Nevius43/Radiation-Detector/Firmware/Radiation_Detector/src/RadScan.png

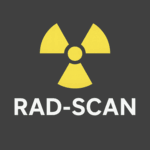
Firmware/Radiation_Detector/src/RadScan.png
