Nevius43/Radiation-Detector/User Interface/SquareLineFiles/cache/thumb_937189207star.png

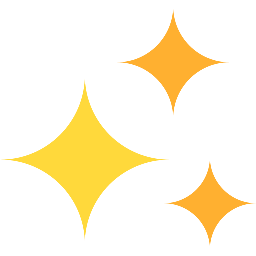
User Interface/SquareLineFiles/cache/thumb_937189207star.png
