Nevius43/Radiation-Detector/User Interface/SquareLineFiles/cache/thumb_1575458026gear.png

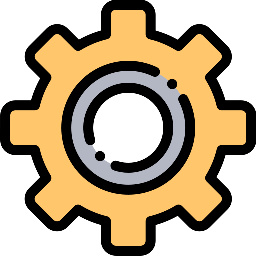
User Interface/SquareLineFiles/cache/thumb_1575458026gear.png
