Nevius43/Radiation-Detector/PCB/RadiationDetector/3D/3314J-1-202E.STEP

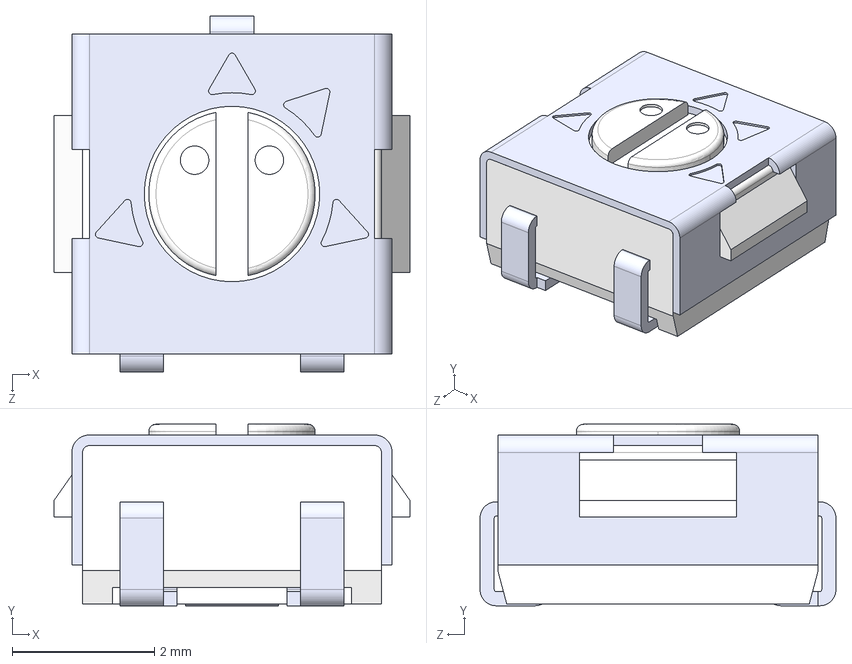
[picture p22: CAD file, 2025-07-28]
PCB/RadiationDetector/3D/3314J-1-202E.STEP
5.00 x 2.55 x 5.00 mm
