Nevius43/Radiation-Detector/PCB/RadiationDetector/3D/PTS645SL43SMTR92-LFS.STEP

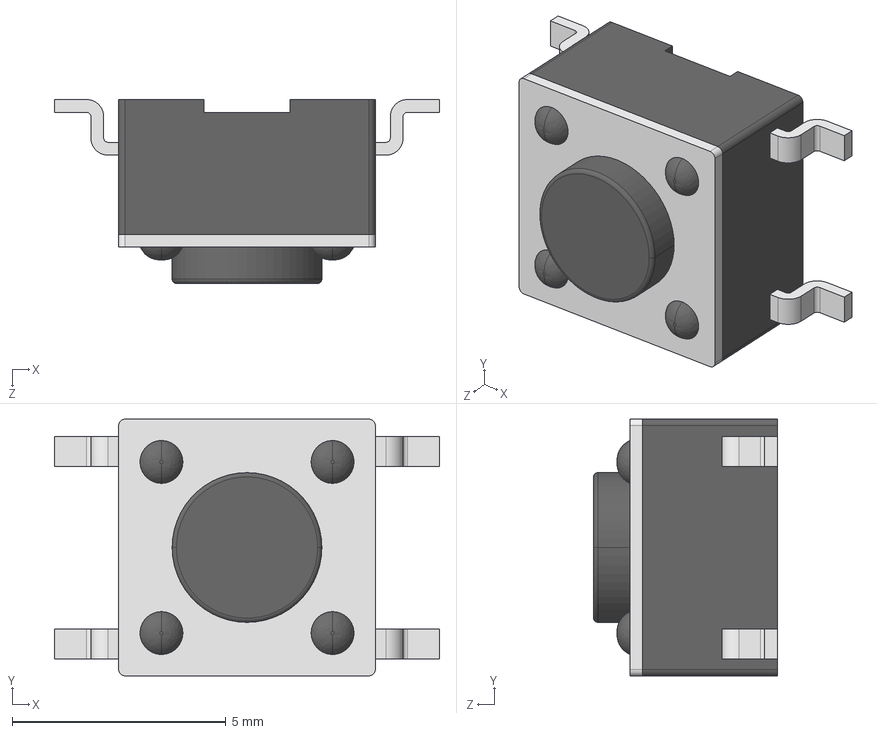
[picture p23: CAD file, 2025-07-28]
PCB/RadiationDetector/3D/PTS645SL43SMTR92-LFS.STEP
9.00 x 6.00 x 4.30 mm
