Nevius43/Radiation-Detector/PCB/RadiationDetector/3D/48102SC.stp

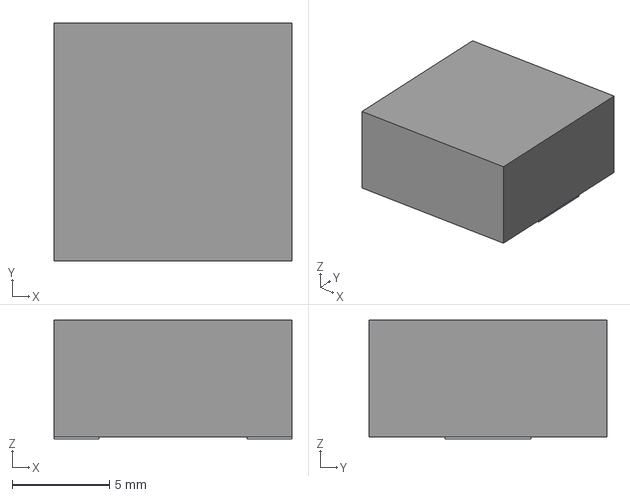
[picture p24: CAD file, 2025-07-28]
PCB/RadiationDetector/3D/48102SC.stp
12.2 x 12.2 x 6.10 mm
Pins
