Nevius43/Radiation-Detector/Firmware/Radiation_Detector/src/ui_font_Pixel.c

/*******************************************************************************
 * Size: 30 px
 * Bpp: 1
 * Opts: --bpp 1 --size 30 --font C:/Users/pablo/OneDrive/Documentos/GitHub/Radiation-Detector/User Interface/SquareLineFiles/assets/VCR_OSD_MONO.ttf -o C:/Users/pablo/OneDrive/Documentos/GitHub/Radiation-Detector/User Interface/SquareLineFiles/assets\ui_font_Pixel.c --format lvgl -r 0x20-0x7f --no-compress --no-prefilter
 ******************************************************************************/

#include "ui.h"

#ifndef UI_FONT_PIXEL
#define UI_FONT_PIXEL 1
#endif

#if UI_FONT_PIXEL

/*-----------------
 *    BITMAPS
 *----------------*/

/*Store the image of the glyphs*/
static LV_ATTRIBUTE_LARGE_CONST const uint8_t glyph_bitmap[] = {
    /* U+0020 " " */
    0x0,

    /* U+0021 "!" */
    0xff, 0xff, 0xff, 0xff, 0xff, 0xf8, 0x3, 0xfe,

    /* U+0022 "\"" */
    0xf0, 0xff, 0xf, 0xf0, 0xff, 0xf, 0x60, 0x66,
    0x6,

    /* U+0023 "#" */
    0x0, 0x70, 0x38, 0xe0, 0x71, 0xc0, 0xe3, 0xf1,
    0xc7, 0xe3, 0xff, 0xff, 0xfc, 0x7f, 0xf8, 0xfc,
    0x70, 0x38, 0xe0, 0x71, 0xf8, 0xe3, 0xf1, 0xff,
    0xff, 0xfe, 0x3f, 0xfc, 0x7e, 0x38, 0x1c, 0x70,
    0x38, 0xe0, 0x70, 0x0,

    /* U+0024 "$" */
    0x3, 0x80, 0x3f, 0xe0, 0x7f, 0xc1, 0xff, 0xc3,
    0xbb, 0x9f, 0x77, 0xfe, 0xef, 0xf1, 0xc7, 0xfb,
    0x80, 0x7f, 0xe0, 0x7f, 0xc0, 0xff, 0xc0, 0x3b,
    0xfc, 0x71, 0xfe, 0xef, 0xfd, 0xdf, 0x3f, 0xf8,
    0x7f, 0xf0, 0x7f, 0xc0, 0x1c, 0x0, 0x38, 0x0,

    /* U+0025 "%" */
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
    0x9e, 0x7, 0xf8, 0x3, 0xf0, 0x7,

    /* U+0079 "y" */
    0xe0, 0xf, 0xc0, 0x1f, 0x80, 0x3f, 0x1, 0xfe,
    0x3, 0xfc, 0x7, 0xf8, 0x1f, 0xfc, 0xff, 0xf9,
    0xfe, 0xff, 0x9c, 0x7e, 0x38, 0xfc, 0x70, 0x0,
    0xe0, 0x7, 0xc0, 0xf, 0x8f, 0xfe, 0x1f, 0xfc,
    0x3f, 0xe0,

    /* U+007A "z" */
    0xff, 0xff, 0xff, 0xff, 0xff, 0xc0, 0xf, 0x0,
    0x78, 0x1, 0xe0, 0xf, 0x0, 0xf0, 0x7, 0x80,
    0x1e, 0x1, 0xe0, 0xf, 0x0, 0x3c, 0x3, 0xff,
    0xff, 0xff, 0xff, 0xff,

    /* U+007B "{" */
    0x7, 0x83, 0xc1, 0xe3, 0xf1, 0xc0, 0xe0, 0x70,
    0x38, 0x1c, 0xe, 0x3c, 0x1e, 0xf, 0x0, 0xe0,
    0x70, 0x38, 0x1c, 0xe, 0x7, 0x3, 0x81, 0xf8,
    0x3c, 0x1e, 0xf,

    /* U+007C "|" */
    0xff, 0xff, 0xff, 0xff, 0xff, 0xff, 0xff, 0xff,
    0xff,

    /* U+007D "}" */
    0xf0, 0x78, 0x3c, 0x1f, 0x81, 0xc0, 0xe0, 0x70,
    0x38, 0x1c, 0xe, 0x1, 0xe0, 0xf0, 0x78, 0xe0,
    0x70, 0x38, 0x1c, 0xe, 0x7, 0x3, 0x8f, 0xc7,
    0x83, 0xc1, 0xe0,

    /* U+007E "~" */
    0x1e, 0x4, 0xfe, 0x73, 0xf9, 0xf9, 0xfc, 0xc0,
    0xe3, 0x3, 0x80
};


/*---------------------
 *  GLYPH DESCRIPTION
 *--------------------*/

static const lv_font_fmt_txt_glyph_dsc_t glyph_dsc[] = {
    {.bitmap_index = 0, .adv_w = 0, .box_w = 0, .box_h = 0, .ofs_x = 0, .ofs_y = 0} /* id = 0 reserved */,
    {.bitmap_index = 0, .adv_w = 281, .box_w = 1, .box_h = 1, .ofs_x = 0, .ofs_y = 0},
    {.bitmap_index = 1, .adv_w = 281, .box_w = 3, .box_h = 21, .ofs_x = 6, .ofs_y = 2},
    {.bitmap_index = 9, .adv_w = 281, .box_w = 12, .box_h = 6, .ofs_x = 3, .ofs_y = 17},
    {.bitmap_index = 18, .adv_w = 281, .box_w = 15, .box_h = 19, .ofs_x = 1, .ofs_y = 4},
    {.bitmap_index = 54, .adv_w = 281, .box_w = 15, .box_h = 21, .ofs_x = 1, .ofs_y = 2},
    {.bitmap_index = 94, .adv_w = 281, .box_w = 15, .box_h = 21, .ofs_x = 1, .ofs_y = 2},
    {.bitmap_index = 134, .adv_w = 281, .box_w = 15, .box_h = 24, .ofs_x = 1, .ofs_y = 2},
    {.bitmap_index = 179, .adv_w = 281, .box_w = 4, .box_h = 6, .ofs_x = 6, .ofs_y = 17},
    {.bitmap_index = 182, .adv_w = 281, .box_w = 7, .box_h = 24, .ofs_x = 4, .ofs_y = 2},
    {.bitmap_index = 203, .adv_w = 281, .box_w = 7, .box_h = 24, .ofs_x = 6, .ofs_y = 2},
    {.bitmap_index = 224, .adv_w = 281, .box_w = 12, .box_h = 13, .ofs_x = 3, .ofs_y = 11},
    {.bitmap_index = 244, .adv_w = 281, .box_w = 15, .box_h = 15, .ofs_x = 1, .ofs_y = 5},
    {.bitmap_index = 273, .adv_w = 281, .box_w = 6, .box_h = 6, .ofs_x = 4, .ofs_y = 2},
    {.bitmap_index = 278, .adv_w = 281, .box_w = 12, .box_h = 3, .ofs_x = 3, .ofs_y = 11},
    {.bitmap_index = 283, .adv_w = 281, .box_w = 3, .box_h = 3, .ofs_x = 6, .ofs_y = 2},
    {.bitmap_index = 285, .adv_w = 281, .box_w = 15, .box_h = 21, .ofs_x = 1, .ofs_y = 2},
    {.bitmap_index = 325, .adv_w = 281, .box_w = 15, .box_h = 21, .ofs_x = 1, .ofs_y = 2},
    {.bitmap_index = 365, .adv_w = 281, .box_w = 9, .box_h = 21, .ofs_x = 4, .ofs_y = 2},
    {.bitmap_index = 389, .adv_w = 281, .box_w = 15, .box_h = 21, .ofs_x = 1, .ofs_y = 2},
    {.bitmap_index = 429, .adv_w = 281, .box_w = 15, .box_h = 21, .ofs_x = 1, .ofs_y = 2},
    {.bitmap_index = 469, .adv_w = 281, .box_w = 15, .box_h = 21, .ofs_x = 1, .ofs_y = 2},
    {.bitmap_index = 509, .adv_w = 281, .box_w = 15, .box_h = 21, .ofs_x = 1, .ofs_y = 2},
    {.bitmap_index = 549, .adv_w = 281, .box_w = 15, .box_h = 21, .ofs_x = 1, .ofs_y = 2},
    {.bitmap_index = 589, .adv_w = 281, .box_w = 15, .box_h = 21, .ofs_x = 1, .ofs_y = 2},
    {.bitmap_index = 629, .adv_w = 281, .box_w = 15, .box_h = 21, .ofs_x = 1, .ofs_y = 2},
    {.bitmap_index = 669, .adv_w = 281, .box_w = 15, .box_h = 21, .ofs_x = 1, .ofs_y = 2},
    {.bitmap_index = 709, .adv_w = 281, .box_w = 3, .box_h = 15, .ofs_x = 6, .ofs_y = 5},
    {.bitmap_index = 715, .adv_w = 281, .box_w = 6, .box_h = 18, .ofs_x = 3, .ofs_y = 1},
    {.bitmap_index = 729, .adv_w = 281, .box_w = 12, .box_h = 23, .ofs_x = 3, .ofs_y = 2},
    {.bitmap_index = 764, .adv_w = 281, .box_w = 15, .box_h = 9, .ofs_x = 1, .ofs_y = 8},
    {.bitmap_index = 781, .adv_w = 281, .box_w = 12, .box_h = 23, .ofs_x = 3, .ofs_y = 2},
    {.bitmap_index = 816, .adv_w = 281, .box_w = 15, .box_h = 21, .ofs_x = 1, .ofs_y = 2},
    {.bitmap_index = 856, .adv_w = 281, .box_w = 15, .box_h = 18, .ofs_x = 1, .ofs_y = 3},
    {.bitmap_index = 890, .adv_w = 281, .box_w = 15, .box_h = 21, .ofs_x = 1, .ofs_y = 2},
    {.bitmap_index = 930, .adv_w = 281, .box_w = 15, .box_h = 21, .ofs_x = 1, .ofs_y = 2},
    {.bitmap_index = 970, .adv_w = 281, .box_w = 15, .box_h = 21, .ofs_x = 1, .ofs_y = 2},
    {.bitmap_index = 1010, .adv_w = 281, .box_w = 15, .box_h = 21, .ofs_x = 1, .ofs_y = 2},
    {.bitmap_index = 1050, .adv_w = 281, .box_w = 15, .box_h = 21, .ofs_x = 1, .ofs_y = 2},
    {.bitmap_index = 1090, .adv_w = 281, .box_w = 15, .box_h = 21, .ofs_x = 1, .ofs_y = 2},
    {.bitmap_index = 1130, .adv_w = 281, .box_w = 15, .box_h = 21, .ofs_x = 1, .ofs_y = 2},
    {.bitmap_index = 1170, .adv_w = 281, .box_w = 15, .box_h = 21, .ofs_x = 1, .ofs_y = 2},
    {.bitmap_index = 1210, .adv_w = 281, .box_w = 9, .box_h = 21, .ofs_x = 4, .ofs_y = 2},
    {.bitmap_index = 1234, .adv_w = 281, .box_w = 15, .box_h = 21, .ofs_x = 1, .ofs_y = 2},
    {.bitmap_index = 1274, .adv_w = 281, .box_w = 15, .box_h = 21, .ofs_x = 1, .ofs_y = 2},
    {.bitmap_index = 1314, .adv_w = 281, .box_w = 15, .box_h = 21, .ofs_x = 1, .ofs_y = 2},
    {.bitmap_index = 1354, .adv_w = 281, .box_w = 15, .box_h = 21, .ofs_x = 1, .ofs_y = 2},
    {.bitmap_index = 1394, .adv_w = 281, .box_w = 15, .box_h = 21, .ofs_x = 1, .ofs_y = 2},
    {.bitmap_index = 1434, .adv_w = 281, .box_w = 15, .box_h = 21, .ofs_x = 1, .ofs_y = 2},
    {.bitmap_index = 1474, .adv_w = 281, .box_w = 15, .box_h = 21, .ofs_x = 1, .ofs_y = 2},
    {.bitmap_index = 1514, .adv_w = 281, .box_w = 15, .box_h = 21, .ofs_x = 1, .ofs_y = 2},
    {.bitmap_index = 1554, .adv_w = 281, .box_w = 15, .box_h = 21, .ofs_x = 1, .ofs_y = 2},
    {.bitmap_index = 1594, .adv_w = 281, .box_w = 15, .box_h = 21, .ofs_x = 1, .ofs_y = 2},
    {.bitmap_index = 1634, .adv_w = 281, .box_w = 15, .box_h = 21, .ofs_x = 1, .ofs_y = 2},
    {.bitmap_index = 1674, .adv_w = 281, .box_w = 15, .box_h = 21, .ofs_x = 1, .ofs_y = 2},
    {.bitmap_index = 1714, .adv_w = 281, .box_w = 15, .box_h = 21, .ofs_x = 1, .ofs_y = 2},
    {.bitmap_index = 1754, .adv_w = 281, .box_w = 15, .box_h = 21, .ofs_x = 1, .ofs_y = 2},
    {.bitmap_index = 1794, .adv_w = 281, .box_w = 15, .box_h = 21, .ofs_x = 1, .ofs_y = 2},
    {.bitmap_index = 1834, .adv_w = 281, .box_w = 15, .box_h = 21, .ofs_x = 1, .ofs_y = 2},
    {.bitmap_index = 1874, .adv_w = 281, .box_w = 15, .box_h = 21, .ofs_x = 1, .ofs_y = 2},
    {.bitmap_index = 1914, .adv_w = 281, .box_w = 9, .box_h = 24, .ofs_x = 6, .ofs_y = 2},
    {.bitmap_index = 1941, .adv_w = 281, .box_w = 15, .box_h = 21, .ofs_x = 1, .ofs_y = 2},
    {.bitmap_index = 1981, .adv_w = 281, .box_w = 9, .box_h = 24, .ofs_x = 3, .ofs_y = 2},
    {.bitmap_index = 2008, .adv_w = 281, .box_w = 14, .box_h = 7, .ofs_x = 1, .ofs_y = 15},
    {.bitmap_index = 2021, .adv_w = 281, .box_w = 18, .box_h = 3, .ofs_x = 0, .ofs_y = 0},
    {.bitmap_index = 2028, .adv_w = 281, .box_w = 7, .box_h = 5, .ofs_x = 4, .ofs_y = 18},
    {.bitmap_index = 2033, .adv_w = 281, .box_w = 15, .box_h = 18, .ofs_x = 1, .ofs_y = 2},
    {.bitmap_index = 2067, .adv_w = 281, .box_w = 15, .box_h = 21, .ofs_x = 1, .ofs_y = 2},
    {.bitmap_index = 2107, .adv_w = 281, .box_w = 15, .box_h = 16, .ofs_x = 1, .ofs_y = 2},
    {.bitmap_index = 2137, .adv_w = 281, .box_w = 15, .box_h = 21, .ofs_x = 1, .ofs_y = 2},
    {.bitmap_index = 2177, .adv_w = 281, .box_w = 14, .box_h = 16, .ofs_x = 1, .ofs_y = 2},
    {.bitmap_index = 2205, .adv_w = 281, .box_w = 12, .box_h = 21, .ofs_x = 3, .ofs_y = 2},
    {.bitmap_index = 2237, .adv_w = 281, .box_w = 15, .box_h = 18, .ofs_x = 1, .ofs_y = 2},
    {.bitmap_index = 2271, .adv_w = 281, .box_w = 15, .box_h = 21, .ofs_x = 1, .ofs_y = 2},
    {.bitmap_index = 2311, .adv_w = 281, .box_w = 9, .box_h = 20, .ofs_x = 4, .ofs_y = 2},
    {.bitmap_index = 2334, .adv_w = 281, .box_w = 9, .box_h = 23, .ofs_x = 4, .ofs_y = 2},
    {.bitmap_index = 2360, .adv_w = 281, .box_w = 15, .box_h = 21, .ofs_x = 1, .ofs_y = 2},
    {.bitmap_index = 2400, .adv_w = 281, .box_w = 3, .box_h = 21, .ofs_x = 7, .ofs_y = 2},
    {.bitmap_index = 2408, .adv_w = 281, .box_w = 15, .box_h = 16, .ofs_x = 1, .ofs_y = 2},
    {.bitmap_index = 2438, .adv_w = 281, .box_w = 15, .box_h = 16, .ofs_x = 1, .ofs_y = 2},
    {.bitmap_index = 2468, .adv_w = 281, .box_w = 15, .box_h = 16, .ofs_x = 1, .ofs_y = 2},
    {.bitmap_index = 2498, .adv_w = 281, .box_w = 15, .box_h = 18, .ofs_x = 1, .ofs_y = 2},
    {.bitmap_index = 2532, .adv_w = 281, .box_w = 15, .box_h = 18, .ofs_x = 1, .ofs_y = 2},
    {.bitmap_index = 2566, .adv_w = 281, .box_w = 15, .box_h = 16, .ofs_x = 1, .ofs_y = 2},
    {.bitmap_index = 2596, .adv_w = 281, .box_w = 14, .box_h = 16, .ofs_x = 1, .ofs_y = 2},
    {.bitmap_index = 2624, .adv_w = 281, .box_w = 9, .box_h = 21, .ofs_x = 4, .ofs_y = 2},
    {.bitmap_index = 2648, .adv_w = 281, .box_w = 15, .box_h = 16, .ofs_x = 1, .ofs_y = 2},
    {.bitmap_index = 2678, .adv_w = 281, .box_w = 15, .box_h = 16, .ofs_x = 1, .ofs_y = 2},
    {.bitmap_index = 2708, .adv_w = 281, .box_w = 15, .box_h = 16, .ofs_x = 1, .ofs_y = 2},
    {.bitmap_index = 2738, .adv_w = 281, .box_w = 15, .box_h = 16, .ofs_x = 1, .ofs_y = 2},
    {.bitmap_index = 2768, .adv_w = 281, .box_w = 15, .box_h = 18, .ofs_x = 1, .ofs_y = 2},
    {.bitmap_index = 2802, .adv_w = 281, .box_w = 14, .box_h = 16, .ofs_x = 1, .ofs_y = 2},
    {.bitmap_index = 2830, .adv_w = 281, .box_w = 9, .box_h = 24, .ofs_x = 4, .ofs_y = 2},
    {.bitmap_index = 2857, .adv_w = 281, .box_w = 3, .box_h = 24, .ofs_x = 7, .ofs_y = 2},
    {.bitmap_index = 2866, .adv_w = 281, .box_w = 9, .box_h = 24, .ofs_x = 4, .ofs_y = 2},
    {.bitmap_index = 2893, .adv_w = 281, .box_w = 14, .box_h = 6, .ofs_x = 1, .ofs_y = 9}
};

/*---------------------
 *  CHARACTER MAPPING
 *--------------------*/



/*Collect the unicode lists and glyph_id offsets*/
static const lv_font_fmt_txt_cmap_t cmaps[] =
{
    {
        .range_start = 32, .range_length = 95, .glyph_id_start = 1,
        .unicode_list = NULL, .glyph_id_ofs_list = NULL, .list_length = 0, .type = LV_FONT_FMT_TXT_CMAP_FORMAT0_TINY
    }
};



/*--------------------
 *  ALL CUSTOM DATA
 *--------------------*/

#if LVGL_VERSION_MAJOR == 8
/*Store all the custom data of the font*/
static  lv_font_fmt_txt_glyph_cache_t cache;
#endif

#if LVGL_VERSION_MAJOR >= 8
static const lv_font_fmt_txt_dsc_t font_dsc = {
#else
static lv_font_fmt_txt_dsc_t font_dsc = {
#endif
    .glyph_bitmap = glyph_bitmap,
    .glyph_dsc = glyph_dsc,
    .cmaps = cmaps,
    .kern_dsc = NULL,
    .kern_scale = 0,
    .cmap_num = 1,
    .bpp = 1,
    .kern_classes = 0,
    .bitmap_format = 0,
#if LVGL_VERSION_MAJOR == 8
    .cache = &cache
#endif
};



/*-----------------
 *  PUBLIC FONT
 *----------------*/

/*Initialize a public general font descriptor*/
#if LVGL_VERSION_MAJOR >= 8
const lv_font_t ui_font_Pixel = {
#else
lv_font_t ui_font_Pixel = {
#endif
    .get_glyph_dsc = lv_font_get_glyph_dsc_fmt_txt,    /*Function pointer to get glyph's data*/
    .get_glyph_bitmap = lv_font_get_bitmap_fmt_txt,    /*Function pointer to get glyph's bitmap*/
    .line_height = 26,          /*The maximum line height required by the font*/
    .base_line = 0,             /*Baseline measured from the bottom of the line*/
#if !(LVGL_VERSION_MAJOR == 6 && LVGL_VERSION_MINOR == 0)
    .subpx = LV_FONT_SUBPX_NONE,
#endif
#if LV_VERSION_CHECK(7, 4, 0) || LVGL_VERSION_MAJOR >= 8
    .underline_position = -3,
    .underline_thickness = 2,
#endif
    .dsc = &font_dsc,          /*The custom font data. Will be accessed by `get_glyph_bitmap/dsc` */
#if LV_VERSION_CHECK(8, 2, 0) || LVGL_VERSION_MAJOR >= 9
    .fallback = NULL,
#endif
    .user_data = NULL,
};



#endif /*#if UI_FONT_PIXEL*/
