Nevius43/Radiation-Detector/Firmware/Radiation_Detector/src/ui_font_Pixel_20.c

/*******************************************************************************
 * Size: 20 px
 * Bpp: 1
 * Opts: --bpp 1 --size 20 --font C:/Users/pablo/OneDrive/Documentos/GitHub/Radiation-Detector/User Interface/SquareLineFiles/assets/VCR_OSD_MONO.ttf -o C:/Users/pablo/OneDrive/Documentos/GitHub/Radiation-Detector/User Interface/SquareLineFiles/assets\ui_font_Pixel_20.c --format lvgl -r 0x20-0x7f --no-compress --no-prefilter
 ******************************************************************************/

#include "ui.h"

#ifndef UI_FONT_PIXEL_20
#define UI_FONT_PIXEL_20 1
#endif

#if UI_FONT_PIXEL_20

/*-----------------
 *    BITMAPS
 *----------------*/

/*Store the image of the glyphs*/
static LV_ATTRIBUTE_LARGE_CONST const uint8_t glyph_bitmap[] = {
    /* U+0020 " " */
    0x0,

    /* U+0021 "!" */
    0xff, 0xff, 0xf0, 0xf0,

    /* U+0022 "\"" */
    0xe7, 0xe7, 0xe7, 0x42,

    /* U+0023 "#" */
    0x3, 0xc, 0xc3, 0x3c, 0xff, 0xff, 0x3c, 0xc3,
    0x30, 0xcf, 0x3f, 0xff, 0xcf, 0x30, 0xcc, 0x30,
    0x0,

    /* U+0024 "$" */
    0xc, 0xf, 0xc7, 0xfb, 0xb7, 0xcc, 0xfb, 0x7,
    0xf0, 0xfe, 0xd, 0xf3, 0x3e, 0xdd, 0xfe, 0x3f,
    0x3, 0x0,

    /* U+0025 "%" */
    0x70, 0xfe, 0x3d, 0x8f, 0x67, 0xfb, 0x9d, 0xc0,
    0xe0, 0x70, 0x3b, 0x9d, 0xfe, 0x6f, 0x1b, 0xc7,
    0xf0, 0xe0,

    /* U+0026 "&" */
    0x1c, 0xf, 0x86, 0x31, 0x8c, 0x63, 0x18, 0xc3,
    0x60, 0xf8, 0x7c, 0x3f, 0xc, 0xef, 0x1f, 0xc3,
    0xb8, 0xe7, 0xfc, 0xfb,

    /* U+0027 "'" */
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

    /* U+007C "|" */
    0xff, 0xff, 0xff, 0xff,

    /* U+007D "}" */
    0xe3, 0x8f, 0xc, 0x30, 0xc3, 0x7, 0x1c, 0xc3,
    0xc, 0x33, 0xce, 0x38,

    /* U+007E "~" */
    0x38, 0x5f, 0x3c, 0xfa, 0x1c
};


/*---------------------
 *  GLYPH DESCRIPTION
 *--------------------*/

static const lv_font_fmt_txt_glyph_dsc_t glyph_dsc[] = {
    {.bitmap_index = 0, .adv_w = 0, .box_w = 0, .box_h = 0, .ofs_x = 0, .ofs_y = 0} /* id = 0 reserved */,
    {.bitmap_index = 0, .adv_w = 188, .box_w = 1, .box_h = 1, .ofs_x = 0, .ofs_y = 0},
    {.bitmap_index = 1, .adv_w = 188, .box_w = 2, .box_h = 14, .ofs_x = 4, .ofs_y = 1},
    {.bitmap_index = 5, .adv_w = 188, .box_w = 8, .box_h = 4, .ofs_x = 2, .ofs_y = 11},
    {.bitmap_index = 9, .adv_w = 188, .box_w = 10, .box_h = 13, .ofs_x = 1, .ofs_y = 2},
    {.bitmap_index = 26, .adv_w = 188, .box_w = 10, .box_h = 14, .ofs_x = 1, .ofs_y = 1},
    {.bitmap_index = 44, .adv_w = 188, .box_w = 10, .box_h = 14, .ofs_x = 1, .ofs_y = 1},
    {.bitmap_index = 62, .adv_w = 188, .box_w = 10, .box_h = 16, .ofs_x = 1, .ofs_y = 1},
    {.bitmap_index = 82, .adv_w = 188, .box_w = 3, .box_h = 4, .ofs_x = 4, .ofs_y = 11},
    {.bitmap_index = 84, .adv_w = 188, .box_w = 5, .box_h = 16, .ofs_x = 3, .ofs_y = 1},
    {.bitmap_index = 94, .adv_w = 188, .box_w = 5, .box_h = 16, .ofs_x = 4, .ofs_y = 1},
    {.bitmap_index = 104, .adv_w = 188, .box_w = 8, .box_h = 9, .ofs_x = 2, .ofs_y = 7},
    {.bitmap_index = 113, .adv_w = 188, .box_w = 10, .box_h = 10, .ofs_x = 1, .ofs_y = 3},
    {.bitmap_index = 126, .adv_w = 188, .box_w = 4, .box_h = 4, .ofs_x = 3, .ofs_y = 1},
    {.bitmap_index = 128, .adv_w = 188, .box_w = 8, .box_h = 2, .ofs_x = 2, .ofs_y = 7},
    {.bitmap_index = 130, .adv_w = 188, .box_w = 2, .box_h = 2, .ofs_x = 4, .ofs_y = 1},
    {.bitmap_index = 131, .adv_w = 188, .box_w = 10, .box_h = 14, .ofs_x = 1, .ofs_y = 1},
    {.bitmap_index = 149, .adv_w = 188, .box_w = 10, .box_h = 14, .ofs_x = 1, .ofs_y = 1},
    {.bitmap_index = 167, .adv_w = 188, .box_w = 6, .box_h = 14, .ofs_x = 3, .ofs_y = 1},
    {.bitmap_index = 178, .adv_w = 188, .box_w = 10, .box_h = 14, .ofs_x = 1, .ofs_y = 1},
    {.bitmap_index = 196, .adv_w = 188, .box_w = 10, .box_h = 14, .ofs_x = 1, .ofs_y = 1},
    {.bitmap_index = 214, .adv_w = 188, .box_w = 10, .box_h = 14, .ofs_x = 1, .ofs_y = 1},
    {.bitmap_index = 232, .adv_w = 188, .box_w = 10, .box_h = 14, .ofs_x = 1, .ofs_y = 1},
    {.bitmap_index = 250, .adv_w = 188, .box_w = 10, .box_h = 14, .ofs_x = 1, .ofs_y = 1},
    {.bitmap_index = 268, .adv_w = 188, .box_w = 10, .box_h = 14, .ofs_x = 1, .ofs_y = 1},
    {.bitmap_index = 286, .adv_w = 188, .box_w = 10, .box_h = 14, .ofs_x = 1, .ofs_y = 1},
    {.bitmap_index = 304, .adv_w = 188, .box_w = 10, .box_h = 14, .ofs_x = 1, .ofs_y = 1},
    {.bitmap_index = 322, .adv_w = 188, .box_w = 2, .box_h = 10, .ofs_x = 4, .ofs_y = 3},
    {.bitmap_index = 325, .adv_w = 188, .box_w = 4, .box_h = 12, .ofs_x = 2, .ofs_y = 1},
    {.bitmap_index = 331, .adv_w = 188, .box_w = 8, .box_h = 15, .ofs_x = 2, .ofs_y = 1},
    {.bitmap_index = 346, .adv_w = 188, .box_w = 10, .box_h = 6, .ofs_x = 1, .ofs_y = 5},
    {.bitmap_index = 354, .adv_w = 188, .box_w = 8, .box_h = 15, .ofs_x = 2, .ofs_y = 1},
    {.bitmap_index = 369, .adv_w = 188, .box_w = 10, .box_h = 14, .ofs_x = 1, .ofs_y = 1},
    {.bitmap_index = 387, .adv_w = 188, .box_w = 10, .box_h = 12, .ofs_x = 1, .ofs_y = 2},
    {.bitmap_index = 402, .adv_w = 188, .box_w = 10, .box_h = 14, .ofs_x = 1, .ofs_y = 1},
    {.bitmap_index = 420, .adv_w = 188, .box_w = 10, .box_h = 14, .ofs_x = 1, .ofs_y = 1},
    {.bitmap_index = 438, .adv_w = 188, .box_w = 10, .box_h = 14, .ofs_x = 1, .ofs_y = 1},
    {.bitmap_index = 456, .adv_w = 188, .box_w = 10, .box_h = 14, .ofs_x = 1, .ofs_y = 1},
    {.bitmap_index = 474, .adv_w = 188, .box_w = 10, .box_h = 14, .ofs_x = 1, .ofs_y = 1},
    {.bitmap_index = 492, .adv_w = 188, .box_w = 10, .box_h = 14, .ofs_x = 1, .ofs_y = 1},
    {.bitmap_index = 510, .adv_w = 188, .box_w = 10, .box_h = 14, .ofs_x = 1, .ofs_y = 1},
    {.bitmap_index = 528, .adv_w = 188, .box_w = 10, .box_h = 14, .ofs_x = 1, .ofs_y = 1},
    {.bitmap_index = 546, .adv_w = 188, .box_w = 6, .box_h = 14, .ofs_x = 3, .ofs_y = 1},
    {.bitmap_index = 557, .adv_w = 188, .box_w = 10, .box_h = 14, .ofs_x = 1, .ofs_y = 1},
    {.bitmap_index = 575, .adv_w = 188, .box_w = 10, .box_h = 14, .ofs_x = 1, .ofs_y = 1},
    {.bitmap_index = 593, .adv_w = 188, .box_w = 10, .box_h = 14, .ofs_x = 1, .ofs_y = 1},
    {.bitmap_index = 611, .adv_w = 188, .box_w = 10, .box_h = 14, .ofs_x = 1, .ofs_y = 1},
    {.bitmap_index = 629, .adv_w = 188, .box_w = 10, .box_h = 14, .ofs_x = 1, .ofs_y = 1},
    {.bitmap_index = 647, .adv_w = 188, .box_w = 10, .box_h = 14, .ofs_x = 1, .ofs_y = 1},
    {.bitmap_index = 665, .adv_w = 188, .box_w = 10, .box_h = 14, .ofs_x = 1, .ofs_y = 1},
    {.bitmap_index = 683, .adv_w = 188, .box_w = 10, .box_h = 14, .ofs_x = 1, .ofs_y = 1},
    {.bitmap_index = 701, .adv_w = 188, .box_w = 10, .box_h = 14, .ofs_x = 1, .ofs_y = 1},
    {.bitmap_index = 719, .adv_w = 188, .box_w = 10, .box_h = 14, .ofs_x = 1, .ofs_y = 1},
    {.bitmap_index = 737, .adv_w = 188, .box_w = 10, .box_h = 14, .ofs_x = 1, .ofs_y = 1},
    {.bitmap_index = 755, .adv_w = 188, .box_w = 10, .box_h = 14, .ofs_x = 1, .ofs_y = 1},
    {.bitmap_index = 773, .adv_w = 188, .box_w = 10, .box_h = 14, .ofs_x = 1, .ofs_y = 1},
    {.bitmap_index = 791, .adv_w = 188, .box_w = 10, .box_h = 14, .ofs_x = 1, .ofs_y = 1},
    {.bitmap_index = 809, .adv_w = 188, .box_w = 10, .box_h = 14, .ofs_x = 1, .ofs_y = 1},
    {.bitmap_index = 827, .adv_w = 188, .box_w = 10, .box_h = 14, .ofs_x = 1, .ofs_y = 1},
    {.bitmap_index = 845, .adv_w = 188, .box_w = 10, .box_h = 14, .ofs_x = 1, .ofs_y = 1},
    {.bitmap_index = 863, .adv_w = 188, .box_w = 6, .box_h = 16, .ofs_x = 4, .ofs_y = 1},
    {.bitmap_index = 875, .adv_w = 188, .box_w = 10, .box_h = 14, .ofs_x = 1, .ofs_y = 1},
    {.bitmap_index = 893, .adv_w = 188, .box_w = 6, .box_h = 16, .ofs_x = 2, .ofs_y = 1},
    {.bitmap_index = 905, .adv_w = 188, .box_w = 10, .box_h = 5, .ofs_x = 1, .ofs_y = 10},
    {.bitmap_index = 912, .adv_w = 188, .box_w = 12, .box_h = 2, .ofs_x = 0, .ofs_y = 0},
    {.bitmap_index = 915, .adv_w = 188, .box_w = 5, .box_h = 3, .ofs_x = 3, .ofs_y = 12},
    {.bitmap_index = 917, .adv_w = 188, .box_w = 10, .box_h = 12, .ofs_x = 1, .ofs_y = 1},
    {.bitmap_index = 932, .adv_w = 188, .box_w = 10, .box_h = 14, .ofs_x = 1, .ofs_y = 1},
    {.bitmap_index = 950, .adv_w = 188, .box_w = 10, .box_h = 11, .ofs_x = 1, .ofs_y = 1},
    {.bitmap_index = 964, .adv_w = 188, .box_w = 10, .box_h = 14, .ofs_x = 1, .ofs_y = 1},
    {.bitmap_index = 982, .adv_w = 188, .box_w = 10, .box_h = 11, .ofs_x = 1, .ofs_y = 1},
    {.bitmap_index = 996, .adv_w = 188, .box_w = 8, .box_h = 14, .ofs_x = 2, .ofs_y = 1},
    {.bitmap_index = 1010, .adv_w = 188, .box_w = 10, .box_h = 12, .ofs_x = 1, .ofs_y = 1},
    {.bitmap_index = 1025, .adv_w = 188, .box_w = 10, .box_h = 14, .ofs_x = 1, .ofs_y = 1},
    {.bitmap_index = 1043, .adv_w = 188, .box_w = 6, .box_h = 13, .ofs_x = 3, .ofs_y = 1},
    {.bitmap_index = 1053, .adv_w = 188, .box_w = 6, .box_h = 15, .ofs_x = 3, .ofs_y = 1},
    {.bitmap_index = 1065, .adv_w = 188, .box_w = 10, .box_h = 14, .ofs_x = 1, .ofs_y = 1},
    {.bitmap_index = 1083, .adv_w = 188, .box_w = 2, .box_h = 14, .ofs_x = 5, .ofs_y = 1},
    {.bitmap_index = 1087, .adv_w = 188, .box_w = 10, .box_h = 11, .ofs_x = 1, .ofs_y = 1},
    {.bitmap_index = 1101, .adv_w = 188, .box_w = 10, .box_h = 11, .ofs_x = 1, .ofs_y = 1},
    {.bitmap_index = 1115, .adv_w = 188, .box_w = 10, .box_h = 11, .ofs_x = 1, .ofs_y = 1},
    {.bitmap_index = 1129, .adv_w = 188, .box_w = 10, .box_h = 12, .ofs_x = 1, .ofs_y = 1},
    {.bitmap_index = 1144, .adv_w = 188, .box_w = 10, .box_h = 12, .ofs_x = 1, .ofs_y = 1},
    {.bitmap_index = 1159, .adv_w = 188, .box_w = 10, .box_h = 11, .ofs_x = 1, .ofs_y = 1},
    {.bitmap_index = 1173, .adv_w = 188, .box_w = 10, .box_h = 11, .ofs_x = 1, .ofs_y = 1},
    {.bitmap_index = 1187, .adv_w = 188, .box_w = 6, .box_h = 14, .ofs_x = 3, .ofs_y = 1},
    {.bitmap_index = 1198, .adv_w = 188, .box_w = 10, .box_h = 11, .ofs_x = 1, .ofs_y = 1},
    {.bitmap_index = 1212, .adv_w = 188, .box_w = 10, .box_h = 11, .ofs_x = 1, .ofs_y = 1},
    {.bitmap_index = 1226, .adv_w = 188, .box_w = 10, .box_h = 11, .ofs_x = 1, .ofs_y = 1},
    {.bitmap_index = 1240, .adv_w = 188, .box_w = 10, .box_h = 11, .ofs_x = 1, .ofs_y = 1},
    {.bitmap_index = 1254, .adv_w = 188, .box_w = 10, .box_h = 12, .ofs_x = 1, .ofs_y = 1},
    {.bitmap_index = 1269, .adv_w = 188, .box_w = 10, .box_h = 11, .ofs_x = 1, .ofs_y = 1},
    {.bitmap_index = 1283, .adv_w = 188, .box_w = 6, .box_h = 16, .ofs_x = 3, .ofs_y = 1},
    {.bitmap_index = 1295, .adv_w = 188, .box_w = 2, .box_h = 16, .ofs_x = 5, .ofs_y = 1},
    {.bitmap_index = 1299, .adv_w = 188, .box_w = 6, .box_h = 16, .ofs_x = 3, .ofs_y = 1},
    {.bitmap_index = 1311, .adv_w = 188, .box_w = 10, .box_h = 4, .ofs_x = 1, .ofs_y = 6}
};

/*---------------------
 *  CHARACTER MAPPING
 *--------------------*/



/*Collect the unicode lists and glyph_id offsets*/
static const lv_font_fmt_txt_cmap_t cmaps[] =
{
    {
        .range_start = 32, .range_length = 95, .glyph_id_start = 1,
        .unicode_list = NULL, .glyph_id_ofs_list = NULL, .list_length = 0, .type = LV_FONT_FMT_TXT_CMAP_FORMAT0_TINY
    }
};



/*--------------------
 *  ALL CUSTOM DATA
 *--------------------*/

#if LVGL_VERSION_MAJOR == 8
/*Store all the custom data of the font*/
static  lv_font_fmt_txt_glyph_cache_t cache;
#endif

#if LVGL_VERSION_MAJOR >= 8
static const lv_font_fmt_txt_dsc_t font_dsc = {
#else
static lv_font_fmt_txt_dsc_t font_dsc = {
#endif
    .glyph_bitmap = glyph_bitmap,
    .glyph_dsc = glyph_dsc,
    .cmaps = cmaps,
    .kern_dsc = NULL,
    .kern_scale = 0,
    .cmap_num = 1,
    .bpp = 1,
    .kern_classes = 0,
    .bitmap_format = 0,
#if LVGL_VERSION_MAJOR == 8
    .cache = &cache
#endif
};



/*-----------------
 *  PUBLIC FONT
 *----------------*/

/*Initialize a public general font descriptor*/
#if LVGL_VERSION_MAJOR >= 8
const lv_font_t ui_font_Pixel_20 = {
#else
lv_font_t ui_font_Pixel_20 = {
#endif
    .get_glyph_dsc = lv_font_get_glyph_dsc_fmt_txt,    /*Function pointer to get glyph's data*/
    .get_glyph_bitmap = lv_font_get_bitmap_fmt_txt,    /*Function pointer to get glyph's bitmap*/
    .line_height = 17,          /*The maximum line height required by the font*/
    .base_line = 0,             /*Baseline measured from the bottom of the line*/
#if !(LVGL_VERSION_MAJOR == 6 && LVGL_VERSION_MINOR == 0)
    .subpx = LV_FONT_SUBPX_NONE,
#endif
#if LV_VERSION_CHECK(7, 4, 0) || LVGL_VERSION_MAJOR >= 8
    .underline_position = -2,
    .underline_thickness = 1,
#endif
    .dsc = &font_dsc,          /*The custom font data. Will be accessed by `get_glyph_bitmap/dsc` */
#if LV_VERSION_CHECK(8, 2, 0) || LVGL_VERSION_MAJOR >= 9
    .fallback = NULL,
#endif
    .user_data = NULL,
};



#endif /*#if UI_FONT_PIXEL_20*/
