Nevius43/Radiation-Detector/Firmware/Radiation_Detector/src/ui_font_Pixel_60.c

/*******************************************************************************
 * Size: 60 px
 * Bpp: 1
 * Opts: --bpp 1 --size 60 --font C:/Users/pablo/OneDrive/Documentos/GitHub/Radiation-Detector/User Interface/SquareLineFiles/assets/VCR_OSD_MONO.ttf -o C:/Users/pablo/OneDrive/Documentos/GitHub/Radiation-Detector/User Interface/SquareLineFiles/assets\ui_font_Pixel_60.c --format lvgl -r 0x20-0x7f --no-compress --no-prefilter
 ******************************************************************************/

#include "ui.h"

#ifndef UI_FONT_PIXEL_60
#define UI_FONT_PIXEL_60 1
#endif

#if UI_FONT_PIXEL_60

/*-----------------
 *    BITMAPS
 *----------------*/

/*Store the image of the glyphs*/
static LV_ATTRIBUTE_LARGE_CONST const uint8_t glyph_bitmap[] = {
    /* U+0020 " " */
    0x0,

    /* U+0021 "!" */
    0xff, 0xff, 0xff, 0xff, 0xff, 0xff, 0xff, 0xff,
    0xff, 0xff, 0xff, 0xff, 0xff, 0xff, 0xff, 0xff,
    0xff, 0xff, 0xff, 0xff, 0xff, 0xfc, 0x0, 0x0,
    0x0, 0x0, 0x3f, 0xff, 0xff, 0xff, 0xfc,

    /* U+0022 "\"" */
    0xff, 0x81, 0xff, 0xff, 0x81, 0xff, 0xff, 0x81,
    0xff, 0xff, 0x81, 0xff, 0xff, 0x81, 0xff, 0xff,
    0x81, 0xff, 0xff, 0x81, 0xff, 0xff, 0x81, 0xff,
    0xff, 0x81, 0xff, 0x1c, 0x0, 0x38, 0x1c, 0x0,
    0x38, 0x1c, 0x0, 0x38,

    /* U+0023 "#" */
    0x0, 0x0, 0x3f, 0x0, 0x0, 0x0, 0xfc, 0x0,
    0x0, 0x3, 0xf0, 0x0, 0xfc, 0xf, 0xc0, 0x3,
    0xf0, 0x3f, 0x0, 0xf, 0xc0, 0xfc, 0x0, 0x3f,
    0x3, 0xff, 0xc0, 0xfc, 0xf, 0xff, 0x3, 0xf0,
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
    0x7, 0xfc,

    /* U+007C "|" */
    0xff, 0xff, 0xff, 0xff, 0xff, 0xff, 0xff, 0xff,
    0xff, 0xff, 0xff, 0xff, 0xff, 0xff, 0xff, 0xff,
    0xff, 0xff, 0xff, 0xff, 0xff, 0xff, 0xff, 0xff,
    0xff, 0xff, 0xff, 0xff, 0xff, 0xff, 0xff, 0xff,
    0xff, 0xff, 0xff, 0xc0,

    /* U+007D "}" */
    0xff, 0x80, 0x3f, 0xe0, 0xf, 0xf8, 0x3, 0xfe,
    0x0, 0xff, 0x80, 0x3f, 0xe0, 0xf, 0xff, 0x3,
    0xff, 0xc0, 0xff, 0xf0, 0x0, 0xfc, 0x0, 0x3f,
    0x0, 0xf, 0xc0, 0x3, 0xf0, 0x0, 0xfc, 0x0,
    0x3f, 0x0, 0xf, 0xc0, 0x3, 0xf0, 0x0, 0xfc,
    0x0, 0x3f, 0x0, 0xf, 0xc0, 0x3, 0xf0, 0x0,
    0x1f, 0xf0, 0x7, 0xfc, 0x1, 0xff, 0x0, 0x7f,
    0xc0, 0x1f, 0xf0, 0x7, 0xfc, 0xf, 0xc0, 0x3,
    0xf0, 0x0, 0xfc, 0x0, 0x3f, 0x0, 0xf, 0xc0,
    0x3, 0xf0, 0x0, 0xfc, 0x0, 0x3f, 0x0, 0xf,
    0xc0, 0x3, 0xf0, 0x0, 0xfc, 0xf, 0xff, 0x3,
    0xff, 0xc0, 0xff, 0xf0, 0x3f, 0xe0, 0xf, 0xf8,
    0x3, 0xfe, 0x0, 0xff, 0x80, 0x3f, 0xe0, 0xf,
    0xf8, 0x0,

    /* U+007E "~" */
    0x3, 0xfe, 0x0, 0x18, 0x1f, 0xf0, 0x0, 0xc0,
    0xff, 0x80, 0x6, 0x3f, 0xff, 0x81, 0xf1, 0xff,
    0xfc, 0xf, 0x8f, 0xff, 0xe0, 0x7f, 0xf0, 0x3f,
    0xff, 0x9f, 0x81, 0xff, 0xfc, 0xfc, 0xf, 0xff,
    0xe7, 0x0, 0xf, 0xf8, 0x38, 0x0, 0x7f, 0xc1,
    0xc0, 0x3, 0xfe, 0x0
};


/*---------------------
 *  GLYPH DESCRIPTION
 *--------------------*/

static const lv_font_fmt_txt_glyph_dsc_t glyph_dsc[] = {
    {.bitmap_index = 0, .adv_w = 0, .box_w = 0, .box_h = 0, .ofs_x = 0, .ofs_y = 0} /* id = 0 reserved */,
    {.bitmap_index = 0, .adv_w = 563, .box_w = 1, .box_h = 1, .ofs_x = 0, .ofs_y = 0},
    {.bitmap_index = 1, .adv_w = 563, .box_w = 6, .box_h = 41, .ofs_x = 12, .ofs_y = 3},
    {.bitmap_index = 32, .adv_w = 563, .box_w = 24, .box_h = 12, .ofs_x = 6, .ofs_y = 32},
    {.bitmap_index = 68, .adv_w = 563, .box_w = 30, .box_h = 38, .ofs_x = 3, .ofs_y = 6},
    {.bitmap_index = 211, .adv_w = 563, .box_w = 29, .box_h = 41, .ofs_x = 3, .ofs_y = 3},
    {.bitmap_index = 360, .adv_w = 563, .box_w = 29, .box_h = 41, .ofs_x = 3, .ofs_y = 3},
    {.bitmap_index = 509, .adv_w = 563, .box_w = 29, .box_h = 47, .ofs_x = 3, .ofs_y = 3},
    {.bitmap_index = 680, .adv_w = 563, .box_w = 9, .box_h = 12, .ofs_x = 12, .ofs_y = 32},
    {.bitmap_index = 694, .adv_w = 563, .box_w = 15, .box_h = 47, .ofs_x = 9, .ofs_y = 3},
    {.bitmap_index = 783, .adv_w = 563, .box_w = 15, .box_h = 47, .ofs_x = 12, .ofs_y = 3},
    {.bitmap_index = 872, .adv_w = 563, .box_w = 23, .box_h = 26, .ofs_x = 6, .ofs_y = 21},
    {.bitmap_index = 947, .adv_w = 563, .box_w = 29, .box_h = 29, .ofs_x = 3, .ofs_y = 9},
    {.bitmap_index = 1053, .adv_w = 563, .box_w = 12, .box_h = 12, .ofs_x = 9, .ofs_y = 3},
    {.bitmap_index = 1071, .adv_w = 563, .box_w = 23, .box_h = 6, .ofs_x = 6, .ofs_y = 20},
    {.bitmap_index = 1089, .adv_w = 563, .box_w = 6, .box_h = 6, .ofs_x = 12, .ofs_y = 3},
    {.bitmap_index = 1094, .adv_w = 563, .box_w = 29, .box_h = 41, .ofs_x = 3, .ofs_y = 3},
    {.bitmap_index = 1243, .adv_w = 563, .box_w = 29, .box_h = 41, .ofs_x = 3, .ofs_y = 3},
    {.bitmap_index = 1392, .adv_w = 563, .box_w = 18, .box_h = 41, .ofs_x = 9, .ofs_y = 3},
    {.bitmap_index = 1485, .adv_w = 563, .box_w = 29, .box_h = 41, .ofs_x = 3, .ofs_y = 3},
    {.bitmap_index = 1634, .adv_w = 563, .box_w = 29, .box_h = 41, .ofs_x = 3, .ofs_y = 3},
    {.bitmap_index = 1783, .adv_w = 563, .box_w = 30, .box_h = 41, .ofs_x = 3, .ofs_y = 3},
    {.bitmap_index = 1937, .adv_w = 563, .box_w = 29, .box_h = 41, .ofs_x = 3, .ofs_y = 3},
    {.bitmap_index = 2086, .adv_w = 563, .box_w = 29, .box_h = 41, .ofs_x = 3, .ofs_y = 3},
    {.bitmap_index = 2235, .adv_w = 563, .box_w = 30, .box_h = 41, .ofs_x = 2, .ofs_y = 3},
    {.bitmap_index = 2389, .adv_w = 563, .box_w = 29, .box_h = 41, .ofs_x = 3, .ofs_y = 3},
    {.bitmap_index = 2538, .adv_w = 563, .box_w = 29, .box_h = 41, .ofs_x = 3, .ofs_y = 3},
    {.bitmap_index = 2687, .adv_w = 563, .box_w = 6, .box_h = 29, .ofs_x = 12, .ofs_y = 9},
    {.bitmap_index = 2709, .adv_w = 563, .box_w = 12, .box_h = 35, .ofs_x = 6, .ofs_y = 3},
    {.bitmap_index = 2762, .adv_w = 563, .box_w = 23, .box_h = 44, .ofs_x = 6, .ofs_y = 3},
    {.bitmap_index = 2889, .adv_w = 563, .box_w = 29, .box_h = 18, .ofs_x = 3, .ofs_y = 15},
    {.bitmap_index = 2955, .adv_w = 563, .box_w = 23, .box_h = 44, .ofs_x = 6, .ofs_y = 3},
    {.bitmap_index = 3082, .adv_w = 563, .box_w = 29, .box_h = 41, .ofs_x = 3, .ofs_y = 3},
    {.bitmap_index = 3231, .adv_w = 563, .box_w = 29, .box_h = 35, .ofs_x = 3, .ofs_y = 6},
    {.bitmap_index = 3358, .adv_w = 563, .box_w = 29, .box_h = 41, .ofs_x = 3, .ofs_y = 3},
    {.bitmap_index = 3507, .adv_w = 563, .box_w = 29, .box_h = 41, .ofs_x = 3, .ofs_y = 3},
    {.bitmap_index = 3656, .adv_w = 563, .box_w = 29, .box_h = 41, .ofs_x = 3, .ofs_y = 3},
    {.bitmap_index = 3805, .adv_w = 563, .box_w = 29, .box_h = 41, .ofs_x = 3, .ofs_y = 3},
    {.bitmap_index = 3954, .adv_w = 563, .box_w = 30, .box_h = 41, .ofs_x = 3, .ofs_y = 3},
    {.bitmap_index = 4108, .adv_w = 563, .box_w = 30, .box_h = 41, .ofs_x = 3, .ofs_y = 3},
    {.bitmap_index = 4262, .adv_w = 563, .box_w = 29, .box_h = 41, .ofs_x = 3, .ofs_y = 3},
    {.bitmap_index = 4411, .adv_w = 563, .box_w = 29, .box_h = 41, .ofs_x = 3, .ofs_y = 3},
    {.bitmap_index = 4560, .adv_w = 563, .box_w = 18, .box_h = 41, .ofs_x = 9, .ofs_y = 3},
    {.bitmap_index = 4653, .adv_w = 563, .box_w = 27, .box_h = 41, .ofs_x = 3, .ofs_y = 3},
    {.bitmap_index = 4792, .adv_w = 563, .box_w = 29, .box_h = 41, .ofs_x = 3, .ofs_y = 3},
    {.bitmap_index = 4941, .adv_w = 563, .box_w = 30, .box_h = 41, .ofs_x = 3, .ofs_y = 3},
    {.bitmap_index = 5095, .adv_w = 563, .box_w = 29, .box_h = 41, .ofs_x = 3, .ofs_y = 3},
    {.bitmap_index = 5244, .adv_w = 563, .box_w = 29, .box_h = 41, .ofs_x = 3, .ofs_y = 3},
    {.bitmap_index = 5393, .adv_w = 563, .box_w = 29, .box_h = 41, .ofs_x = 3, .ofs_y = 3},
    {.bitmap_index = 5542, .adv_w = 563, .box_w = 29, .box_h = 41, .ofs_x = 3, .ofs_y = 3},
    {.bitmap_index = 5691, .adv_w = 563, .box_w = 29, .box_h = 41, .ofs_x = 3, .ofs_y = 3},
    {.bitmap_index = 5840, .adv_w = 563, .box_w = 29, .box_h = 41, .ofs_x = 3, .ofs_y = 3},
    {.bitmap_index = 5989, .adv_w = 563, .box_w = 29, .box_h = 41, .ofs_x = 3, .ofs_y = 3},
    {.bitmap_index = 6138, .adv_w = 563, .box_w = 29, .box_h = 41, .ofs_x = 3, .ofs_y = 3},
    {.bitmap_index = 6287, .adv_w = 563, .box_w = 29, .box_h = 41, .ofs_x = 3, .ofs_y = 3},
    {.bitmap_index = 6436, .adv_w = 563, .box_w = 29, .box_h = 41, .ofs_x = 3, .ofs_y = 3},
    {.bitmap_index = 6585, .adv_w = 563, .box_w = 29, .box_h = 41, .ofs_x = 3, .ofs_y = 3},
    {.bitmap_index = 6734, .adv_w = 563, .box_w = 29, .box_h = 41, .ofs_x = 3, .ofs_y = 3},
    {.bitmap_index = 6883, .adv_w = 563, .box_w = 29, .box_h = 41, .ofs_x = 3, .ofs_y = 3},
    {.bitmap_index = 7032, .adv_w = 563, .box_w = 29, .box_h = 41, .ofs_x = 3, .ofs_y = 3},
    {.bitmap_index = 7181, .adv_w = 563, .box_w = 18, .box_h = 47, .ofs_x = 12, .ofs_y = 3},
    {.bitmap_index = 7287, .adv_w = 563, .box_w = 29, .box_h = 41, .ofs_x = 3, .ofs_y = 3},
    {.bitmap_index = 7436, .adv_w = 563, .box_w = 18, .box_h = 47, .ofs_x = 5, .ofs_y = 3},
    {.bitmap_index = 7542, .adv_w = 563, .box_w = 29, .box_h = 15, .ofs_x = 3, .ofs_y = 29},
    {.bitmap_index = 7597, .adv_w = 563, .box_w = 35, .box_h = 6, .ofs_x = 0, .ofs_y = 0},
    {.bitmap_index = 7624, .adv_w = 563, .box_w = 15, .box_h = 9, .ofs_x = 9, .ofs_y = 35},
    {.bitmap_index = 7641, .adv_w = 563, .box_w = 29, .box_h = 35, .ofs_x = 3, .ofs_y = 3},
    {.bitmap_index = 7768, .adv_w = 563, .box_w = 29, .box_h = 41, .ofs_x = 3, .ofs_y = 3},
    {.bitmap_index = 7917, .adv_w = 563, .box_w = 29, .box_h = 32, .ofs_x = 3, .ofs_y = 3},
    {.bitmap_index = 8033, .adv_w = 563, .box_w = 29, .box_h = 41, .ofs_x = 3, .ofs_y = 3},
    {.bitmap_index = 8182, .adv_w = 563, .box_w = 29, .box_h = 32, .ofs_x = 3, .ofs_y = 3},
    {.bitmap_index = 8298, .adv_w = 563, .box_w = 24, .box_h = 41, .ofs_x = 6, .ofs_y = 3},
    {.bitmap_index = 8421, .adv_w = 563, .box_w = 29, .box_h = 35, .ofs_x = 3, .ofs_y = 3},
    {.bitmap_index = 8548, .adv_w = 563, .box_w = 29, .box_h = 41, .ofs_x = 3, .ofs_y = 3},
    {.bitmap_index = 8697, .adv_w = 563, .box_w = 18, .box_h = 38, .ofs_x = 9, .ofs_y = 3},
    {.bitmap_index = 8783, .adv_w = 563, .box_w = 18, .box_h = 44, .ofs_x = 9, .ofs_y = 3},
    {.bitmap_index = 8882, .adv_w = 563, .box_w = 29, .box_h = 41, .ofs_x = 3, .ofs_y = 3},
    {.bitmap_index = 9031, .adv_w = 563, .box_w = 6, .box_h = 41, .ofs_x = 15, .ofs_y = 3},
    {.bitmap_index = 9062, .adv_w = 563, .box_w = 29, .box_h = 32, .ofs_x = 3, .ofs_y = 3},
    {.bitmap_index = 9178, .adv_w = 563, .box_w = 29, .box_h = 32, .ofs_x = 3, .ofs_y = 3},
    {.bitmap_index = 9294, .adv_w = 563, .box_w = 29, .box_h = 32, .ofs_x = 3, .ofs_y = 3},
    {.bitmap_index = 9410, .adv_w = 563, .box_w = 29, .box_h = 35, .ofs_x = 3, .ofs_y = 3},
    {.bitmap_index = 9537, .adv_w = 563, .box_w = 29, .box_h = 35, .ofs_x = 3, .ofs_y = 3},
    {.bitmap_index = 9664, .adv_w = 563, .box_w = 29, .box_h = 32, .ofs_x = 3, .ofs_y = 3},
    {.bitmap_index = 9780, .adv_w = 563, .box_w = 29, .box_h = 32, .ofs_x = 3, .ofs_y = 3},
    {.bitmap_index = 9896, .adv_w = 563, .box_w = 18, .box_h = 41, .ofs_x = 9, .ofs_y = 3},
    {.bitmap_index = 9989, .adv_w = 563, .box_w = 29, .box_h = 32, .ofs_x = 3, .ofs_y = 3},
    {.bitmap_index = 10105, .adv_w = 563, .box_w = 29, .box_h = 32, .ofs_x = 3, .ofs_y = 3},
    {.bitmap_index = 10221, .adv_w = 563, .box_w = 29, .box_h = 32, .ofs_x = 3, .ofs_y = 3},
    {.bitmap_index = 10337, .adv_w = 563, .box_w = 29, .box_h = 32, .ofs_x = 3, .ofs_y = 3},
    {.bitmap_index = 10453, .adv_w = 563, .box_w = 29, .box_h = 35, .ofs_x = 3, .ofs_y = 3},
    {.bitmap_index = 10580, .adv_w = 563, .box_w = 29, .box_h = 32, .ofs_x = 3, .ofs_y = 3},
    {.bitmap_index = 10696, .adv_w = 563, .box_w = 18, .box_h = 47, .ofs_x = 9, .ofs_y = 3},
    {.bitmap_index = 10802, .adv_w = 563, .box_w = 6, .box_h = 47, .ofs_x = 15, .ofs_y = 3},
    {.bitmap_index = 10838, .adv_w = 563, .box_w = 18, .box_h = 47, .ofs_x = 9, .ofs_y = 3},
    {.bitmap_index = 10944, .adv_w = 563, .box_w = 29, .box_h = 12, .ofs_x = 3, .ofs_y = 18}
};

/*---------------------
 *  CHARACTER MAPPING
 *--------------------*/



/*Collect the unicode lists and glyph_id offsets*/
static const lv_font_fmt_txt_cmap_t cmaps[] =
{
    {
        .range_start = 32, .range_length = 95, .glyph_id_start = 1,
        .unicode_list = NULL, .glyph_id_ofs_list = NULL, .list_length = 0, .type = LV_FONT_FMT_TXT_CMAP_FORMAT0_TINY
    }
};



/*--------------------
 *  ALL CUSTOM DATA
 *--------------------*/

#if LVGL_VERSION_MAJOR == 8
/*Store all the custom data of the font*/
static  lv_font_fmt_txt_glyph_cache_t cache;
#endif

#if LVGL_VERSION_MAJOR >= 8
static const lv_font_fmt_txt_dsc_t font_dsc = {
#else
static lv_font_fmt_txt_dsc_t font_dsc = {
#endif
    .glyph_bitmap = glyph_bitmap,
    .glyph_dsc = glyph_dsc,
    .cmaps = cmaps,
    .kern_dsc = NULL,
    .kern_scale = 0,
    .cmap_num = 1,
    .bpp = 1,
    .kern_classes = 0,
    .bitmap_format = 0,
#if LVGL_VERSION_MAJOR == 8
    .cache = &cache
#endif
};



/*-----------------
 *  PUBLIC FONT
 *----------------*/

/*Initialize a public general font descriptor*/
#if LVGL_VERSION_MAJOR >= 8
const lv_font_t ui_font_Pixel_60 = {
#else
lv_font_t ui_font_Pixel_60 = {
#endif
    .get_glyph_dsc = lv_font_get_glyph_dsc_fmt_txt,    /*Function pointer to get glyph's data*/
    .get_glyph_bitmap = lv_font_get_bitmap_fmt_txt,    /*Function pointer to get glyph's bitmap*/
    .line_height = 50,          /*The maximum line height required by the font*/
    .base_line = 0,             /*Baseline measured from the bottom of the line*/
#if !(LVGL_VERSION_MAJOR == 6 && LVGL_VERSION_MINOR == 0)
    .subpx = LV_FONT_SUBPX_NONE,
#endif
#if LV_VERSION_CHECK(7, 4, 0) || LVGL_VERSION_MAJOR >= 8
    .underline_position = -6,
    .underline_thickness = 4,
#endif
    .dsc = &font_dsc,          /*The custom font data. Will be accessed by `get_glyph_bitmap/dsc` */
#if LV_VERSION_CHECK(8, 2, 0) || LVGL_VERSION_MAJOR >= 9
    .fallback = NULL,
#endif
    .user_data = NULL,
};



#endif /*#if UI_FONT_PIXEL_60*/
