Nevius43/Radiation-Detector/Firmware/Radiation_Detector/src/ui_font_SonicSaber.c

/*******************************************************************************
 * Size: 28 px
 * Bpp: 1
 * Opts: --bpp 1 --size 28 --font C:/Users/pablo/OneDrive/Documentos/GitHub/Geiger_Counter/SquareLineFiles/assets/SonicSaberPersonalUse-Regular.ttf -o C:/Users/pablo/OneDrive/Documentos/GitHub/Geiger_Counter/SquareLineFiles/assets\ui_font_SonicSaber.c --format lvgl -r 0x20-0x7f --no-compress --no-prefilter
 ******************************************************************************/

#include "ui.h"

#ifndef UI_FONT_SONICSABER
#define UI_FONT_SONICSABER 1
#endif

#if UI_FONT_SONICSABER

/*-----------------
 *    BITMAPS
 *----------------*/

/*Store the image of the glyphs*/
static LV_ATTRIBUTE_LARGE_CONST const uint8_t glyph_bitmap[] = {
    /* U+0020 " " */
    0x0,

    /* U+0021 "!" */
    0x6f, 0xff, 0xff, 0xff, 0xff, 0xff, 0xff, 0xf6,
    0xf, 0xff,

    /* U+0022 "\"" */
    0xed, 0xfb, 0xf3, 0x6c, 0xc0,

    /* U+0023 "#" */
    0x6, 0x60, 0xf, 0xf0, 0xf, 0xf0, 0xf, 0xf0,
    0xff, 0xff, 0xff, 0xff, 0xff, 0xff, 0xf, 0xf0,
    0xf, 0xf0, 0xff, 0xff, 0xff, 0xff, 0xff, 0xff,
    0xf, 0xf0, 0xf, 0xf0, 0xf, 0xf0, 0x6, 0x60,

    /* U+0024 "$" */
    0x3, 0x0, 0x3c, 0x1, 0xe0, 0xf, 0x3, 0xfe,
    0x3f, 0xfb, 0xff, 0xfe, 0xff, 0xf7, 0xff, 0xbd,
    0xbd, 0xe1, 0xff, 0xc7, 0xff, 0x1f, 0xfc, 0x1f,
    0xe0, 0xff, 0x7, 0xff, 0xbf, 0xfd, 0xff, 0xef,
    0xff, 0xff, 0xbf, 0xf8, 0xff, 0x80, 0xf0, 0x3,
    0x80,

    /* U+0025 "%" */
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
    0xe0, 0xfc, 0x1f, 0x3, 0xc0, 0x78, 0xf, 0x1,
    0xe0, 0x3c, 0x7, 0x8f, 0xf1, 0xfe, 0x3f, 0xc0,

    /* U+007E "~" */
    0x1e, 0x0, 0xfe, 0x1f, 0xff, 0x7f, 0xff, 0xfe,
    0x3f, 0xc8, 0x1f, 0x0
};


/*---------------------
 *  GLYPH DESCRIPTION
 *--------------------*/

static const lv_font_fmt_txt_glyph_dsc_t glyph_dsc[] = {
    {.bitmap_index = 0, .adv_w = 0, .box_w = 0, .box_h = 0, .ofs_x = 0, .ofs_y = 0} /* id = 0 reserved */,
    {.bitmap_index = 0, .adv_w = 152, .box_w = 1, .box_h = 1, .ofs_x = 0, .ofs_y = 0},
    {.bitmap_index = 1, .adv_w = 83, .box_w = 4, .box_h = 20, .ofs_x = 1, .ofs_y = 1},
    {.bitmap_index = 11, .adv_w = 140, .box_w = 7, .box_h = 5, .ofs_x = 1, .ofs_y = 17},
    {.bitmap_index = 16, .adv_w = 285, .box_w = 16, .box_h = 16, .ofs_x = 1, .ofs_y = 2},
    {.bitmap_index = 48, .adv_w = 239, .box_w = 13, .box_h = 25, .ofs_x = 1, .ofs_y = -2},
    {.bitmap_index = 89, .adv_w = 287, .box_w = 16, .box_h = 24, .ofs_x = 1, .ofs_y = -2},
    {.bitmap_index = 137, .adv_w = 274, .box_w = 16, .box_h = 21, .ofs_x = 1, .ofs_y = 0},
    {.bitmap_index = 179, .adv_w = 83, .box_w = 3, .box_h = 5, .ofs_x = 1, .ofs_y = 17},
    {.bitmap_index = 181, .adv_w = 137, .box_w = 7, .box_h = 23, .ofs_x = 1, .ofs_y = -2},
    {.bitmap_index = 202, .adv_w = 137, .box_w = 8, .box_h = 23, .ofs_x = 0, .ofs_y = -2},
    {.bitmap_index = 225, .adv_w = 231, .box_w = 13, .box_h = 16, .ofs_x = 0, .ofs_y = 2},
    {.bitmap_index = 251, .adv_w = 285, .box_w = 16, .box_h = 16, .ofs_x = 1, .ofs_y = 2},
    {.bitmap_index = 283, .adv_w = 83, .box_w = 3, .box_h = 5, .ofs_x = 1, .ofs_y = -2},
    {.bitmap_index = 285, .adv_w = 213, .box_w = 11, .box_h = 3, .ofs_x = 1, .ofs_y = 7},
    {.bitmap_index = 290, .adv_w = 83, .box_w = 4, .box_h = 3, .ofs_x = 1, .ofs_y = -1},
    {.bitmap_index = 292, .adv_w = 214, .box_w = 11, .box_h = 23, .ofs_x = 1, .ofs_y = -1},
    {.bitmap_index = 324, .adv_w = 296, .box_w = 17, .box_h = 20, .ofs_x = 1, .ofs_y = 0},
    {.bitmap_index = 367, .adv_w = 192, .box_w = 11, .box_h = 21, .ofs_x = 1, .ofs_y = 0},
    {.bitmap_index = 396, .adv_w = 295, .box_w = 17, .box_h = 21, .ofs_x = 1, .ofs_y = 0},
    {.bitmap_index = 441, .adv_w = 280, .box_w = 16, .box_h = 21, .ofs_x = 1, .ofs_y = 0},
    {.bitmap_index = 483, .adv_w = 289, .box_w = 17, .box_h = 21, .ofs_x = 1, .ofs_y = 0},
    {.bitmap_index = 528, .adv_w = 271, .box_w = 15, .box_h = 21, .ofs_x = 1, .ofs_y = 0},
    {.bitmap_index = 568, .adv_w = 267, .box_w = 15, .box_h = 21, .ofs_x = 1, .ofs_y = 0},
    {.bitmap_index = 608, .adv_w = 250, .box_w = 15, .box_h = 21, .ofs_x = 1, .ofs_y = 0},
    {.bitmap_index = 648, .adv_w = 281, .box_w = 16, .box_h = 21, .ofs_x = 1, .ofs_y = 0},
    {.bitmap_index = 690, .adv_w = 266, .box_w = 15, .box_h = 21, .ofs_x = 1, .ofs_y = 0},
    {.bitmap_index = 730, .adv_w = 84, .box_w = 4, .box_h = 7, .ofs_x = 1, .ofs_y = 6},
    {.bitmap_index = 734, .adv_w = 85, .box_w = 3, .box_h = 9, .ofs_x = 1, .ofs_y = 4},
    {.bitmap_index = 738, .adv_w = 193, .box_w = 10, .box_h = 15, .ofs_x = 1, .ofs_y = 2},
    {.bitmap_index = 757, .adv_w = 213, .box_w = 11, .box_h = 9, .ofs_x = 1, .ofs_y = 5},
    {.bitmap_index = 770, .adv_w = 193, .box_w = 10, .box_h = 15, .ofs_x = 1, .ofs_y = 2},
    {.bitmap_index = 789, .adv_w = 217, .box_w = 12, .box_h = 21, .ofs_x = 1, .ofs_y = 0},
    {.bitmap_index = 821, .adv_w = 342, .box_w = 20, .box_h = 19, .ofs_x = 1, .ofs_y = 0},
    {.bitmap_index = 869, .adv_w = 327, .box_w = 19, .box_h = 21, .ofs_x = 0, .ofs_y = 0},
    {.bitmap_index = 919, .adv_w = 315, .box_w = 18, .box_h = 21, .ofs_x = 0, .ofs_y = 0},
    {.bitmap_index = 967, .adv_w = 317, .box_w = 18, .box_h = 21, .ofs_x = 0, .ofs_y = 0},
    {.bitmap_index = 1015, .adv_w = 334, .box_w = 19, .box_h = 21, .ofs_x = 0, .ofs_y = 0},
    {.bitmap_index = 1065, .adv_w = 316, .box_w = 18, .box_h = 21, .ofs_x = 1, .ofs_y = 0},
    {.bitmap_index = 1113, .adv_w = 297, .box_w = 17, .box_h = 21, .ofs_x = 0, .ofs_y = 0},
    {.bitmap_index = 1158, .adv_w = 319, .box_w = 18, .box_h = 21, .ofs_x = 0, .ofs_y = 0},
    {.bitmap_index = 1206, .adv_w = 316, .box_w = 18, .box_h = 21, .ofs_x = 1, .ofs_y = 0},
    {.bitmap_index = 1254, .adv_w = 100, .box_w = 5, .box_h = 21, .ofs_x = 1, .ofs_y = 0},
    {.bitmap_index = 1268, .adv_w = 280, .box_w = 16, .box_h = 21, .ofs_x = 0, .ofs_y = 0},
    {.bitmap_index = 1310, .adv_w = 295, .box_w = 17, .box_h = 21, .ofs_x = 0, .ofs_y = 0},
    {.bitmap_index = 1355, .adv_w = 281, .box_w = 16, .box_h = 21, .ofs_x = 0, .ofs_y = 0},
    {.bitmap_index = 1397, .adv_w = 383, .box_w = 22, .box_h = 21, .ofs_x = 0, .ofs_y = 0},
    {.bitmap_index = 1455, .adv_w = 317, .box_w = 18, .box_h = 21, .ofs_x = 0, .ofs_y = 0},
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
    {.bitmap_index = 3215, .adv_w = 84, .box_w = 3, .box_h = 24, .ofs_x = 1, .ofs_y = -3},
    {.bitmap_index = 3224, .adv_w = 197, .box_w = 11, .box_h = 23, .ofs_x = 1, .ofs_y = -2},
    {.bitmap_index = 3256, .adv_w = 278, .box_w = 15, .box_h = 6, .ofs_x = 1, .ofs_y = 6}
};

/*---------------------
 *  CHARACTER MAPPING
 *--------------------*/



/*Collect the unicode lists and glyph_id offsets*/
static const lv_font_fmt_txt_cmap_t cmaps[] =
{
    {
        .range_start = 32, .range_length = 95, .glyph_id_start = 1,
        .unicode_list = NULL, .glyph_id_ofs_list = NULL, .list_length = 0, .type = LV_FONT_FMT_TXT_CMAP_FORMAT0_TINY
    }
};

/*-----------------
 *    KERNING
 *----------------*/


/*Pair left and right glyphs for kerning*/
static const uint8_t kern_pair_glyph_ids[] =
{
    17, 18,
    17, 19,
    17, 20,
    17, 22,
    17, 23,
    17, 24,
    17, 25,
    17, 26,
    18, 17,
    18, 19,
    18, 20,
    18, 22,
    18, 23,
    18, 24,
    18, 25,
    18, 26,
    19, 17,
    19, 21,
    19, 22,
    19, 23,
    19, 24,
    19, 25,
    19, 26,
    20, 17,
    20, 18,
    20, 19,
    20, 21,
    20, 22,
    20, 24,
    20, 25,
    21, 17,
    21, 18,
    21, 19,
    21, 20,
    21, 21,
    21, 22,
    21, 23,
    21, 24,
    21, 25,
    21, 26,
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
};

/* Kerning between the respective left and right glyphs
 * 4.4 format which needs to scaled with `kern_scale`*/
static const int8_t kern_pair_values[] =
{
    -20, -2, -4, -2, -2, -22, -2, -2,
    7, 2, 2, 2, 2, 2, 2, 4,
    -7, -26, -2, -11, -4, -4, -2, -2,
    -4, -2, -4, -2, -13, -2, -2, -22,
    -20, -13, -2, -9, -2, -20, -2, -15,
    -15, -2, -4, -15, -2, -24, -11, -2,
    -13, -24, -24, -2, -9, -13, -52, -11,
    -44, -15, -13, -11, -2, 2, -11, -9,
    -4, -2, -15, -4, -24, -9, -4, -2,
    -2, -2, -2, -2, -2, -2, -2, -2,
    -68, -7, -66, -22, -66, -2, -22, -44,
    -2, -48, -2, -46, -2, -2, -2, -2,
    -11, -2, -4, -42, -4, -4, -44, -20,
    -9, -22, -9, -2, -17, -50, -2, -48,
    -70, -59, -2, -52, -4, -2, -42, -42,
    -42, -2, -44, -4, -2, -48, -2, -2,
    -4, -2, -4, -2, -4, -4, -2, -2,
    -4, -2, -72, -4, -66, -20, -68, 2,
    -2, -4, -4, -2, -22, -52, -50, -2,
    -66, -2, -2, -2, -2, -42, -44, -4,
    -46, -55, -2, -66, -9, -4, -2, -4,
    -7, -2, -7, -4, -4, -4, -7, -2,
    -2, -2, -48, -2, -2, -2, -4, -4,
    -7, -7, -2, -2, -2, -4, -2, -4,
    -7, -4, -4, -4, -44, -2, -2, -9,
    -2, -4, -44, -4, -2, -4, -42, -68,
    -2, -4, -68, -2, -7, -2, -2, -44,
    -44, -46, -44, -26, -42, -57, -42, -42,
    -42, -42, -39, -39, -42, -24, -42, -42,
    -42, -44, -42, -46, -42, -63, -4, -4,
    -4, -2, -55, 2, -2, -4, -7, -2,
    -2, -2, -20, -2, -11, -13, -13, -15,
    -13, -48, -11, -15, -15, -13, -15, -11,
    -17, -15, -9, -13, -15, -13, -11, -13,
    -28, -17, -2, -11, -7, -7, -9, -13,
    -7, -42, -4, -7, -7, -4, -4, -4,
    -7, -7, -4, -7, -7, -4, -4, -7,
    -42, -66, -2, -61, -2, -2, -2, -4,
    -26, -28, -26, -24, -24, -20, -48, -22,
    -22, -22, -22, -22, -22, -22, -24, -17,
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
};

/*Collect the kern pair's data in one place*/
static const lv_font_fmt_txt_kern_pair_t kern_pairs =
{
    .glyph_ids = kern_pair_glyph_ids,
    .values = kern_pair_values,
    .pair_cnt = 349,
    .glyph_ids_size = 0
};

/*--------------------
 *  ALL CUSTOM DATA
 *--------------------*/

#if LVGL_VERSION_MAJOR == 8
/*Store all the custom data of the font*/
static  lv_font_fmt_txt_glyph_cache_t cache;
#endif

#if LVGL_VERSION_MAJOR >= 8
static const lv_font_fmt_txt_dsc_t font_dsc = {
#else
static lv_font_fmt_txt_dsc_t font_dsc = {
#endif
    .glyph_bitmap = glyph_bitmap,
    .glyph_dsc = glyph_dsc,
    .cmaps = cmaps,
    .kern_dsc = &kern_pairs,
    .kern_scale = 16,
    .cmap_num = 1,
    .bpp = 1,
    .kern_classes = 0,
    .bitmap_format = 0,
#if LVGL_VERSION_MAJOR == 8
    .cache = &cache
#endif
};



/*-----------------
 *  PUBLIC FONT
 *----------------*/

/*Initialize a public general font descriptor*/
#if LVGL_VERSION_MAJOR >= 8
const lv_font_t ui_font_SonicSaber = {
#else
lv_font_t ui_font_SonicSaber = {
#endif
    .get_glyph_dsc = lv_font_get_glyph_dsc_fmt_txt,    /*Function pointer to get glyph's data*/
    .get_glyph_bitmap = lv_font_get_bitmap_fmt_txt,    /*Function pointer to get glyph's bitmap*/
    .line_height = 29,          /*The maximum line height required by the font*/
    .base_line = 6,             /*Baseline measured from the bottom of the line*/
#if !(LVGL_VERSION_MAJOR == 6 && LVGL_VERSION_MINOR == 0)
    .subpx = LV_FONT_SUBPX_NONE,
#endif
#if LV_VERSION_CHECK(7, 4, 0) || LVGL_VERSION_MAJOR >= 8
    .underline_position = -1,
    .underline_thickness = 1,
#endif
    .dsc = &font_dsc,          /*The custom font data. Will be accessed by `get_glyph_bitmap/dsc` */
#if LV_VERSION_CHECK(8, 2, 0) || LVGL_VERSION_MAJOR >= 9
    .fallback = NULL,
#endif
    .user_data = NULL,
};



#endif /*#if UI_FONT_SONICSABER*/
